SloBloLabs/PhonoAmp/img/SSA_C105_2u2.png

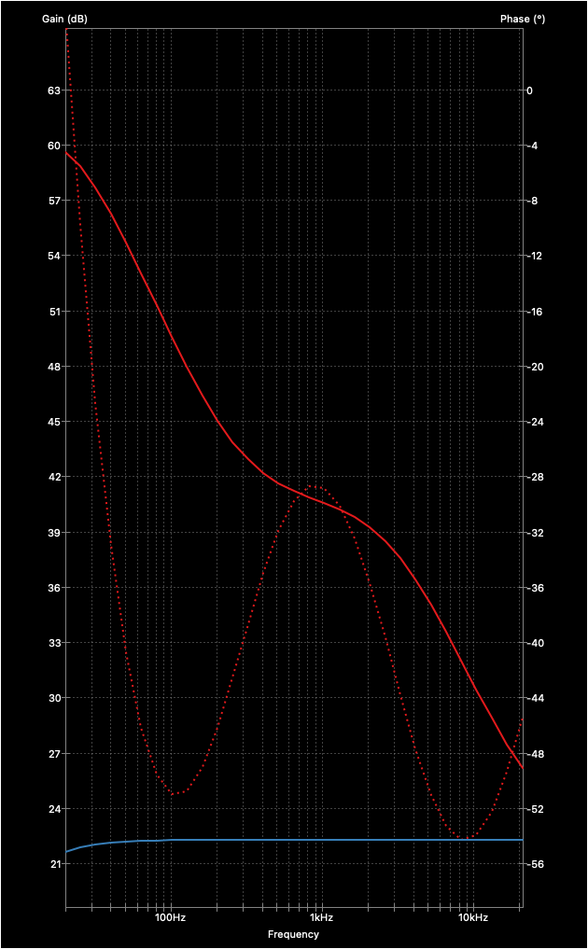
img/SSA_C105_2u2.png
